GioSunrider/OmniRobot/PCB/PCB_OmniRobot.kicad_pcb

## KiCad design CAD_files/syringe_pump/encoder/encoder.sch

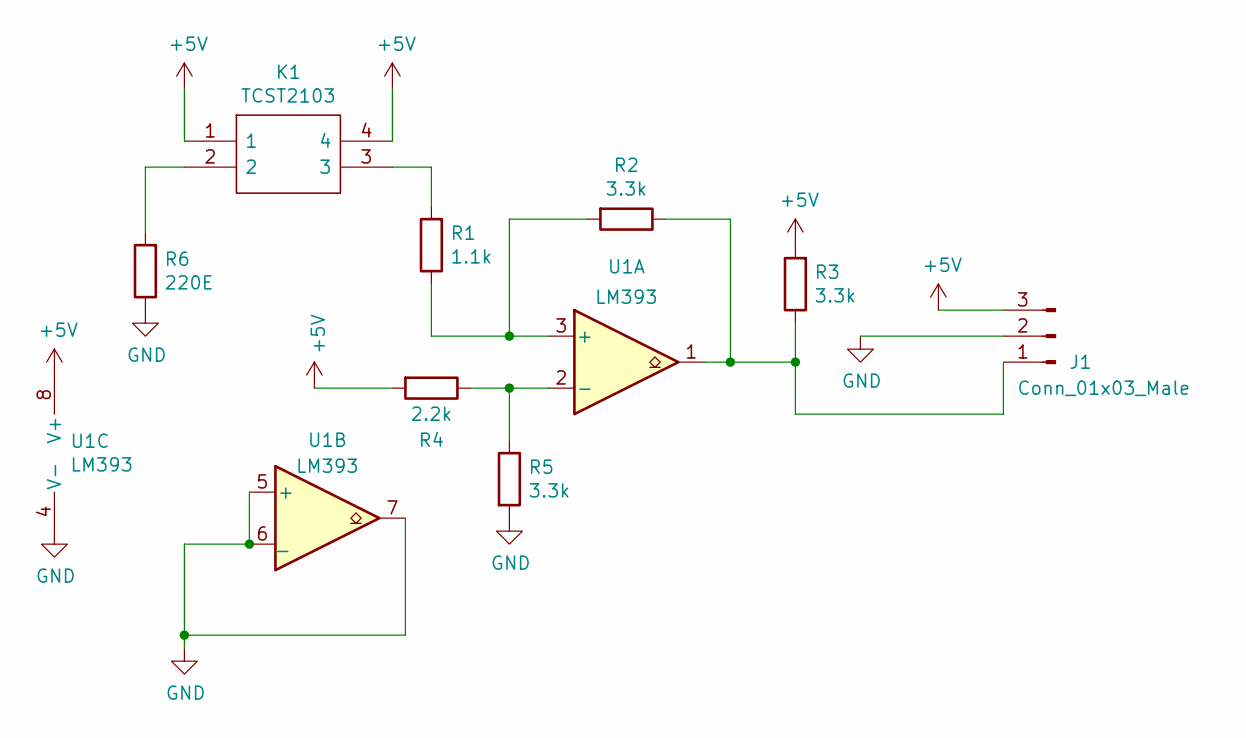
[picture p17: schematic encoder.sch]

Parts:
J1: Conn_01x03_Male
K1: TCST2103; DIPS254W40P760L2450H1110Q4N; Manufacturer_Part_Number TCST2103; Mouser Part Number 782-TCST2103
R1: 1.1k
R2, R3, R5: 3.3k
R4: 2.2k
R6: 220E
U1: LM393

Connections:
+5V: J1.3, K1.1, K1.4, R3.2, R4.2, U1.8 (V+)
GND: J1.2, R5.2, R6.1, U1.4 (V-), U1.5 (+), U1.6 (_), U1.7
unnamed: J1.1, R2.1, R3.1, U1.1
unnamed: K1.2, R6.2
unnamed: K1.3, R1.2
unnamed: R1.1, R2.2, U1.3 (+)
unnamed: R4.1, R5.1, U1.2 (-)
